Keyman-Taiwan/ErgoDoxTW/preview/v1.4_LeftHand_Top.png

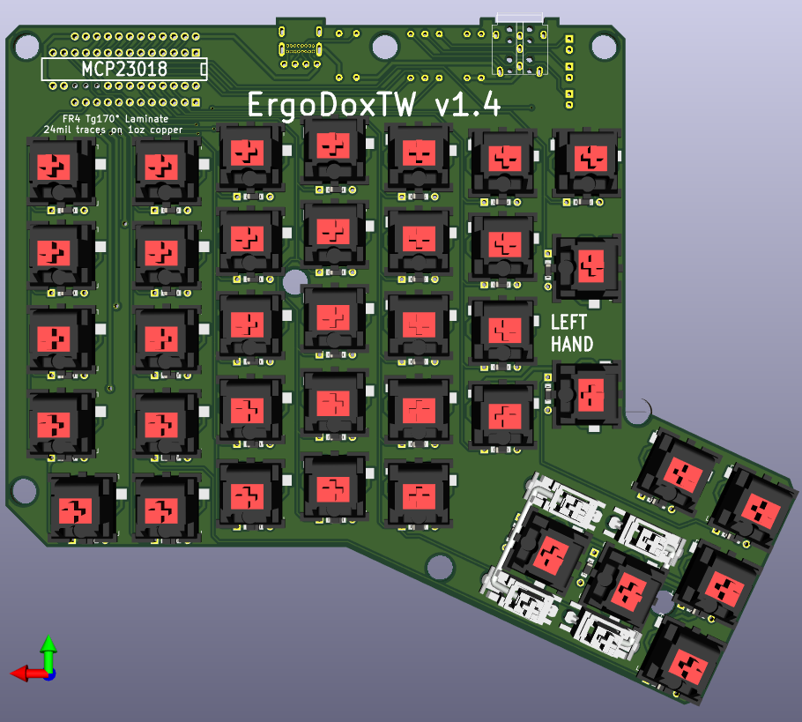
preview/v1.4_LeftHand_Top.png
