Keyman-Taiwan/ErgoDoxTW/ref_data/3.5mm/PJ-320E_5p.jpg

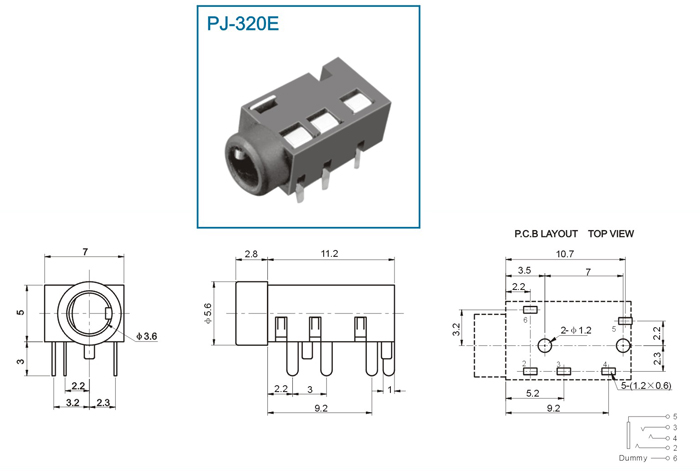
ref_data/3.5mm/PJ-320E_5p.jpg
